A4091/a4091-collateral/a4091_3kled/A4091_3KLED.kicad_sch

## KiCad design a4091_3kled/A4091_3KLED.kicad_sch (2023-09-26)

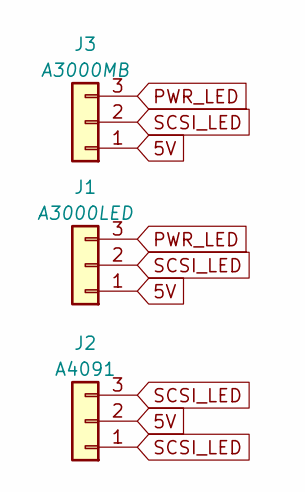
[picture p19: schematic A4091_3KLED.kicad_sch]

Parts:
J1: A3000LED; Pins_1x03_2.54mm_TH_AudioInsRGndL; Part Number 1-0301FBV0T
J2: A4091; Pins_1x03_2.54mm_TH_AudioInsRGndL; Part Number 1-0301FBV0T
J3: A3000MB; Pins_1x03_2.54mm_TH_AudioInsRGndL; Part Number 1-0301FBV0T

Connections:
5V: J1.1, J2.2, J3.1
PWR_LED: J1.3, J3.3
SCSI_LED: J1.2, J2.1, J2.3, J3.2
